LogicElements/matter-lora-env-node/firmware/stm32/Core/Inc/DEV_Config.h

/*****************************************************************************
* | File      	:   DEV_Config.h
* | Author      :   Waveshare team
* | Function    :   Hardware underlying interface
* | Info        :
*                Used to shield the underlying layers of each master 
*                and enhance portability
*----------------
* |	This version:   V2.0
* | Date        :   2018-10-30
* | Info        :
* 1.add:
*   UBYTE\UWORD\UDOUBLE
* 2.Change:
*   EPD_RST -> EPD_RST_PIN
*   EPD_DC -> EPD_DC_PIN
*   EPD_CS -> EPD_CS_PIN
*   EPD_BUSY -> EPD_BUSY_PIN
* 3.Remote:
*   EPD_RST_1\EPD_RST_0
*   EPD_DC_1\EPD_DC_0
*   EPD_CS_1\EPD_CS_0
*   EPD_BUSY_1\EPD_BUSY_0
* 3.add:
*   #define DEV_Digital_Write(_pin, _value) bcm2835_gpio_write(_pin, _value)
*   #define DEV_Digital_Read(_pin) bcm2835_gpio_lev(_pin)
*   #define DEV_SPI_WriteByte(__value) bcm2835_spi_transfer(__value)
#
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
******************************************************************************/
#ifndef _DEV_CONFIG_H_
#define _DEV_CONFIG_H_

#include "main.h"
#include "stm32u0xx_hal.h"
#include "stm32u0xx_hal_gpio.h"
#include <stdint.h>
#include <stdio.h>

/**
 * data
**/
#define UBYTE   uint8_t
#define UWORD   uint16_t
#define UDOUBLE uint32_t

/**
 * e-Paper GPIO
**/
#define EPD_RST_PIN     EPD_RST_GPIO_Port, EPD_RST_Pin
#define EPD_DC_PIN      EPD_DC_GPIO_Port, EPD_DC_Pin
#define EPD_PWR_PIN     PS4_GPIO_Port, PS4_Pin
#define EPD_CS_PIN      EPD_CS_GPIO_Port, EPD_CS_Pin
#define EPD_BUSY_PIN    EPD_BUSY_GPIO_Port, EPD_BUSY_Pin
#define EPD_MOSI_PIN    EPD_DIN_GPIO_Port, EPD_DIN_Pin
#define EPD_SCLK_PIN    EPD_SCK_GPIO_Port, EPD_SCK_Pin

/**
 * GPIO read and write
**/
#define DEV_Digital_Write(_pin, _value) HAL_GPIO_WritePin(_pin, _value == 0? GPIO_PIN_RESET:GPIO_PIN_SET)
#define DEV_Digital_Read(_pin) HAL_GPIO_ReadPin(_pin)

/**
 * delay x ms
**/
#define DEV_Delay_ms(__xms) HAL_Delay(__xms);

void DEV_SPI_WriteByte(UBYTE value);
void DEV_SPI_Write_nByte(UBYTE *value, UDOUBLE len);

int DEV_Module_Init(void);
void EPD_Pins_HiZ(void);
void EPD_Pins_Init(void);
void DEV_Module_Exit(void);
void DEV_GPIO_Init(void);
void DEV_SPI_Init(void);
void DEV_SPI_SendData(UBYTE Reg);
UBYTE DEV_SPI_ReadData(void);
#endif
