LogicElements/matter-lora-env-node/firmware/stm32/Core/Src/images.c

/*
 * images.c
 *
 *  Created on: Sep 12, 2025
 *      Author: evzen
 */

#include "images.h"

const unsigned char epd_bitmap_dead_hot[] = {
		0xff, 0xff, 0xff, 0xff, 0xff, 0x9f, 0xc0, 0xff, 0xff, 0xe0, 0x03, 0xff, 0x0f, 0xc0, 0xff, 0xff,
		0x00, 0x00, 0x3e, 0x07, 0xc0, 0xff, 0xf8, 0x00, 0x00, 0x0c, 0x07, 0xc0, 0xff, 0xf0, 0x00, 0x00,
		0x00, 0x03, 0xc0, 0xff, 0xc0, 0x07, 0xf8, 0x00, 0x01, 0xc0, 0xff, 0x80, 0x7f, 0xff, 0x00, 0x41,
		0xc0, 0xff, 0x01, 0xff, 0xff, 0xe0, 0x60, 0xc0, 0xfe, 0x07, 0xff, 0xff, 0xe0, 0xf0, 0xc0, 0xfc,
		0x0f, 0xff, 0xff, 0xe1, 0xf0, 0x40, 0xf8, 0x1f, 0xff, 0xff, 0xe1, 0xf8, 0x40, 0xf0, 0x3f, 0xff,
		0xff, 0xc1, 0xf8, 0x40, 0xf0, 0x7f, 0xff, 0xff, 0xc3, 0xf8, 0x00, 0xe0, 0xff, 0xff, 0xff, 0xc3,
		0xf8, 0x00, 0xe0, 0xff, 0xff, 0xff, 0xc1, 0xf8, 0x40, 0xc1, 0xff, 0xff, 0xff, 0xe1, 0xf8, 0x40,
		0xc3, 0xc7, 0xc7, 0xf8, 0xe0, 0x60, 0x40, 0xc3, 0x83, 0x87, 0xf0, 0x60, 0x00, 0xc0, 0x83, 0x81,
		0x03, 0xf0, 0x20, 0x00, 0xc0, 0x87, 0xc0, 0x07, 0xf8, 0x00, 0x00, 0xc0, 0x87, 0xc0, 0x0f, 0xfc,
		0x00, 0x00, 0x40, 0x87, 0xe0, 0x1f, 0xfe, 0x03, 0xf8, 0x40, 0x87, 0xf0, 0x1f, 0xfe, 0x03, 0xf8,
		0x40, 0x07, 0xe0, 0x0f, 0xfc, 0x01, 0xf8, 0x40, 0x07, 0xc0, 0x07, 0xf8, 0x00, 0xf8, 0x40, 0x07,
		0x80, 0x07, 0xf0, 0x00, 0x78, 0x40, 0x07, 0x83, 0x03, 0xf0, 0x70, 0x78, 0x40, 0x07, 0x87, 0xc7,
		0xf8, 0xf8, 0xf8, 0x40, 0x07, 0xff, 0xff, 0xff, 0xff, 0xf8, 0x40, 0x87, 0xff, 0xff, 0xff, 0xff,
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
		0xff, 0xff, 0xff, 0x8f, 0x1f, 0xff, 0xff, 0xf0, 0xff, 0xff, 0xff, 0x8f, 0x1f, 0xff, 0xff, 0xf0,
		0xff, 0xff, 0xff, 0x80, 0x1f, 0xff, 0xff, 0xf0, 0xff, 0xff, 0xff, 0x80, 0x1f, 0xff, 0xff, 0xf0,
		0xff, 0xff, 0xff, 0xff, 0xff, 0xff, 0xff, 0xf0, 0xff, 0xff, 0xff, 0xff, 0xff, 0xff, 0xff, 0xf0
};
