LogicElements/matter-lora-env-node/firmware/stm32/Core/Inc/images.h

/*
 * images.h
 *
 *  Created on: Sep 12, 2025
 *      Author: evzen
 */

#ifndef INC_IMAGES_H_
#define INC_IMAGES_H_

#include <stdint.h>

extern const unsigned char epd_bitmap_dead_hot[];
extern const unsigned char epd_bitmap_dead_basic[];
extern const unsigned char epd_bitmap_dead_cold[];
extern const unsigned char epd_bitmap_happy_basic[];
extern const unsigned char epd_bitmap_happy_cold[];
extern const unsigned char epd_bitmap_happy_hot[];
extern const unsigned char epd_bitmap_neutral_basic[];
extern const unsigned char epd_bitmap_neutral_cold[];
extern const unsigned char epd_bitmap_neutral_hot[];
extern const unsigned char epd_bitmap_sad_basic[];
extern const unsigned char epd_bitmap_sad_cold[];
extern const unsigned char epd_bitmap_sad_hot[];

extern const unsigned char gImage_ThreadOK[];
extern const unsigned char gImage_ThreadNot[];
extern const unsigned char gImage_LoraOK[];
extern const unsigned char gImage_LoraNot[];

extern const unsigned char ConfigureIcon[];

#endif /* INC_IMAGES_H_ */
